jsyk/Talking_Clock/doc/cpuboard_pcb.png

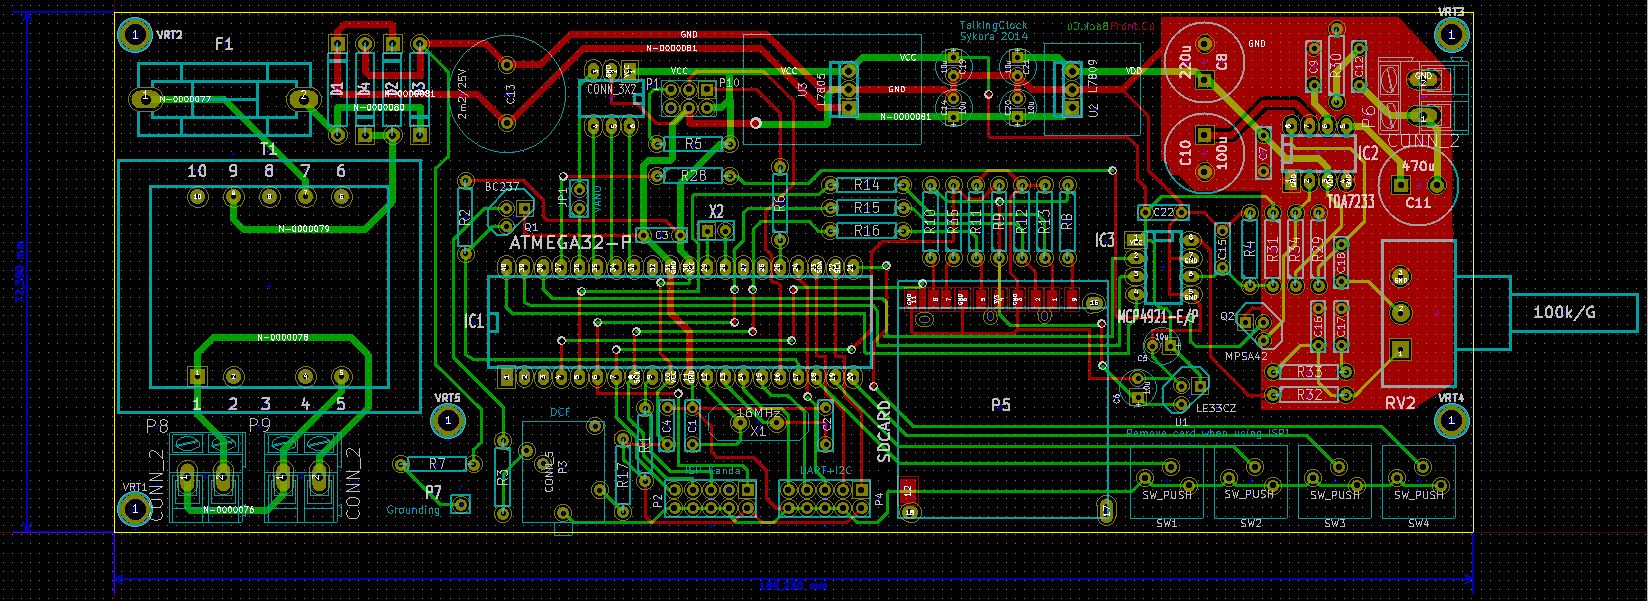
doc/cpuboard_pcb.png
