jsyk/Talking_Clock/doc/cpuboard_sch_atmega.png

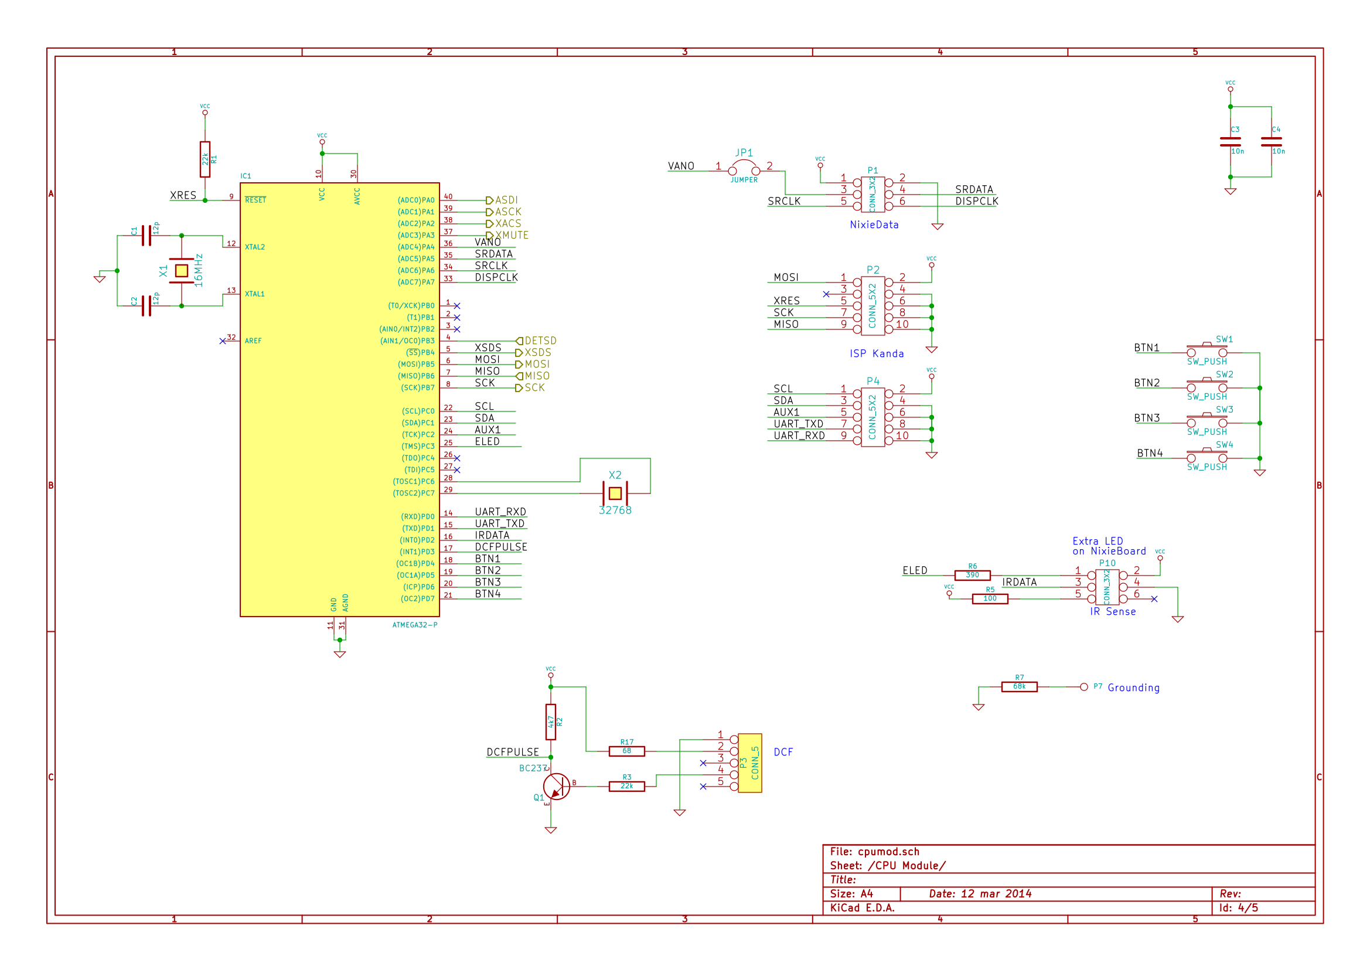
doc/cpuboard_sch_atmega.png
