jsyk/Talking_Clock/doc/cpuboard_sch_power.png

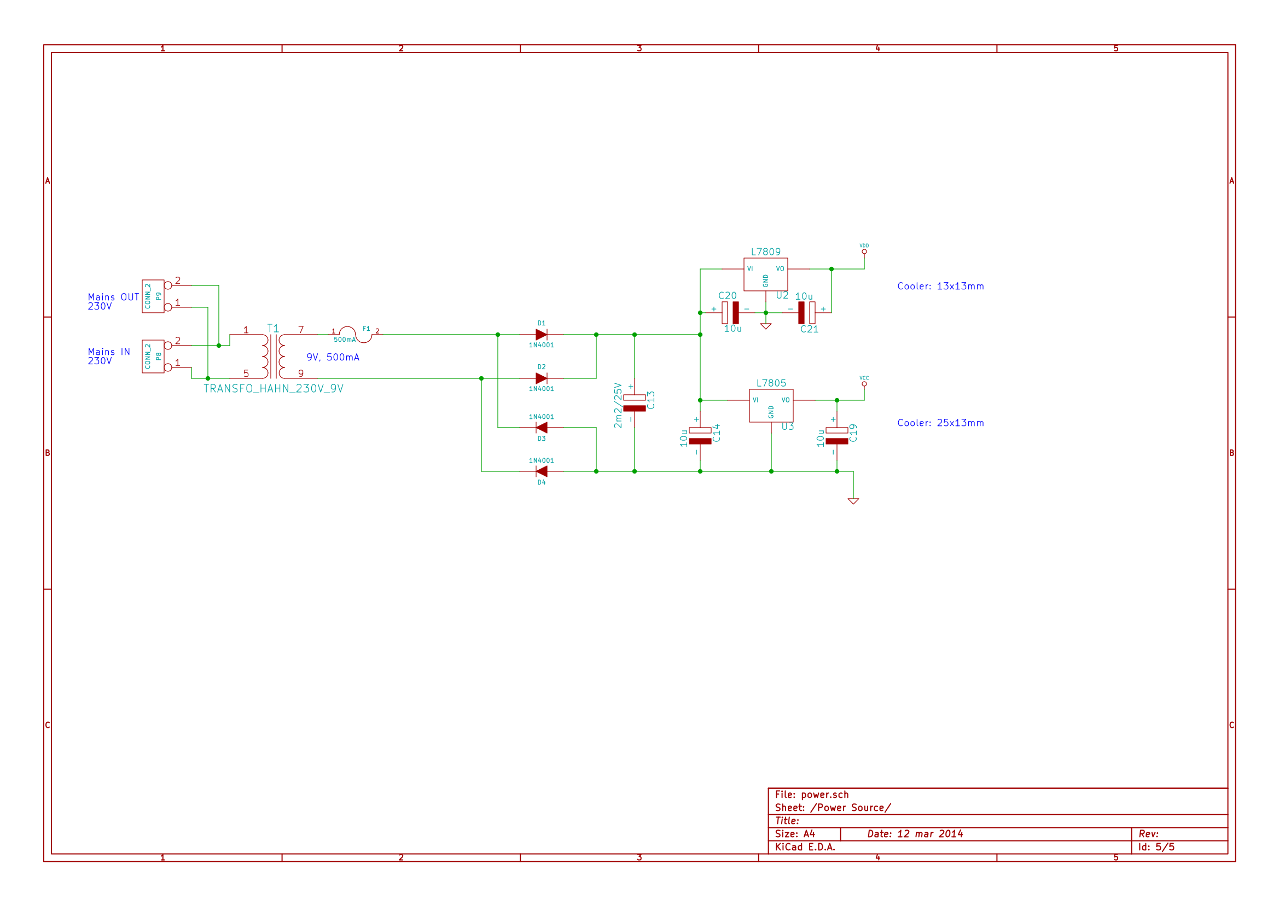
doc/cpuboard_sch_power.png
