jsyk/Talking_Clock/doc/cpuboard_sch_sdcard.png

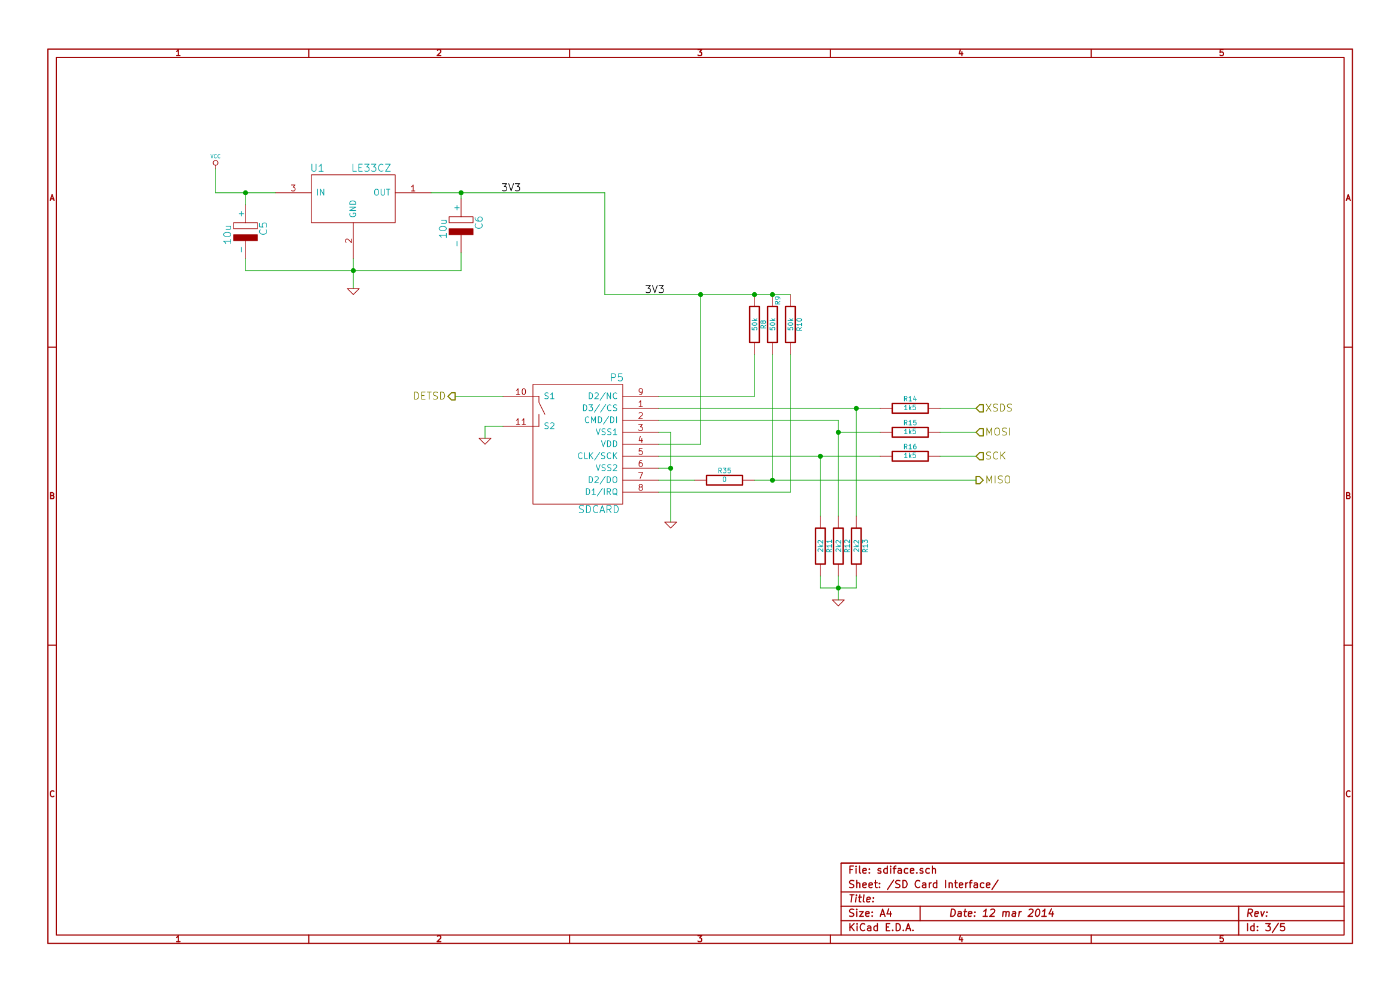
doc/cpuboard_sch_sdcard.png
