jsyk/Talking_Clock/doc/cpuboard_sch_soundsynth.png

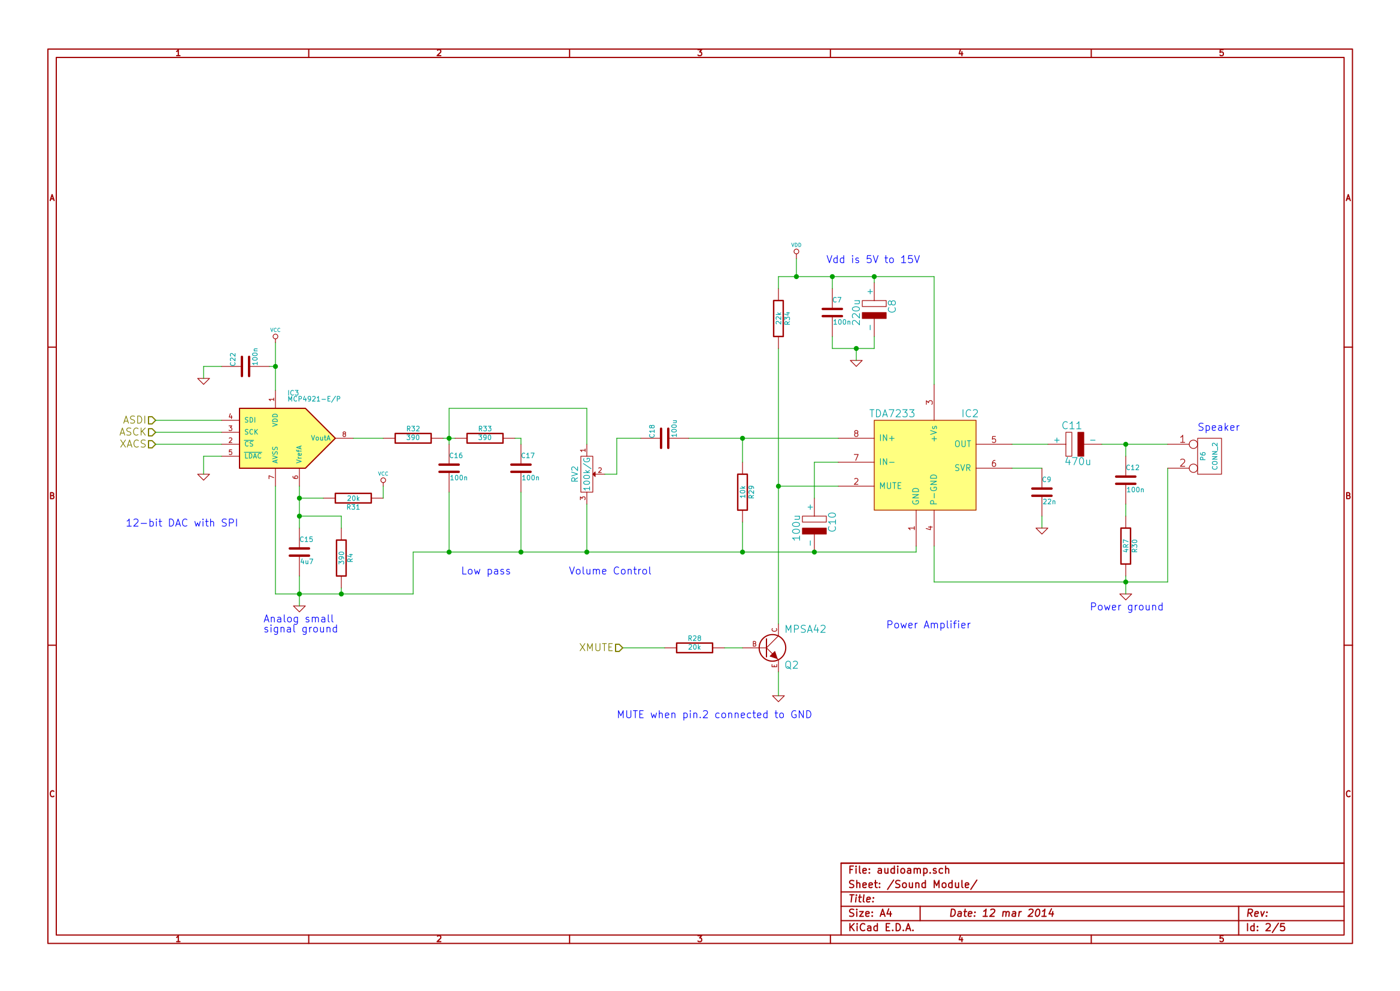
doc/cpuboard_sch_soundsynth.png
