jsyk/Talking_Clock/doc/nixieboard_pcb.png

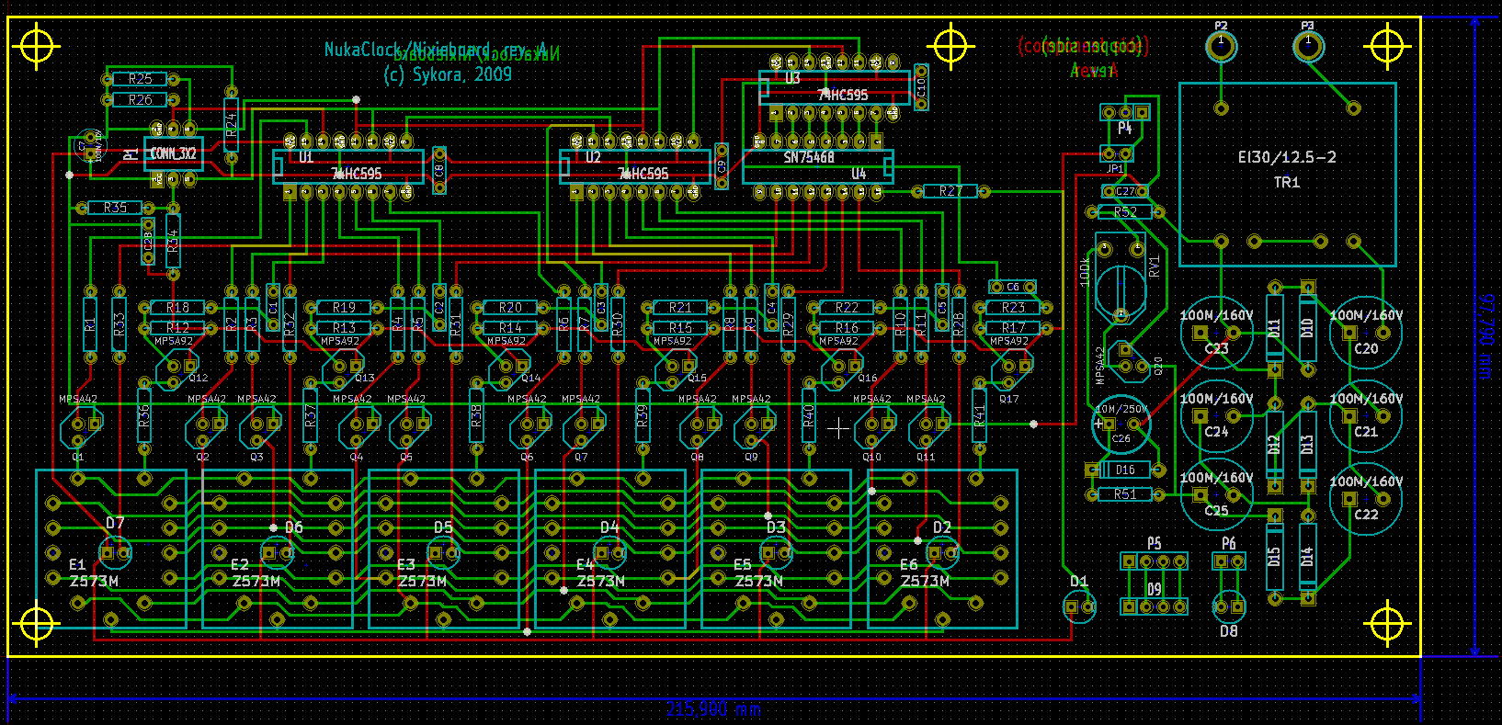
doc/nixieboard_pcb.png
