jsyk/Talking_Clock/doc/nixieboard_sch_drivers.png

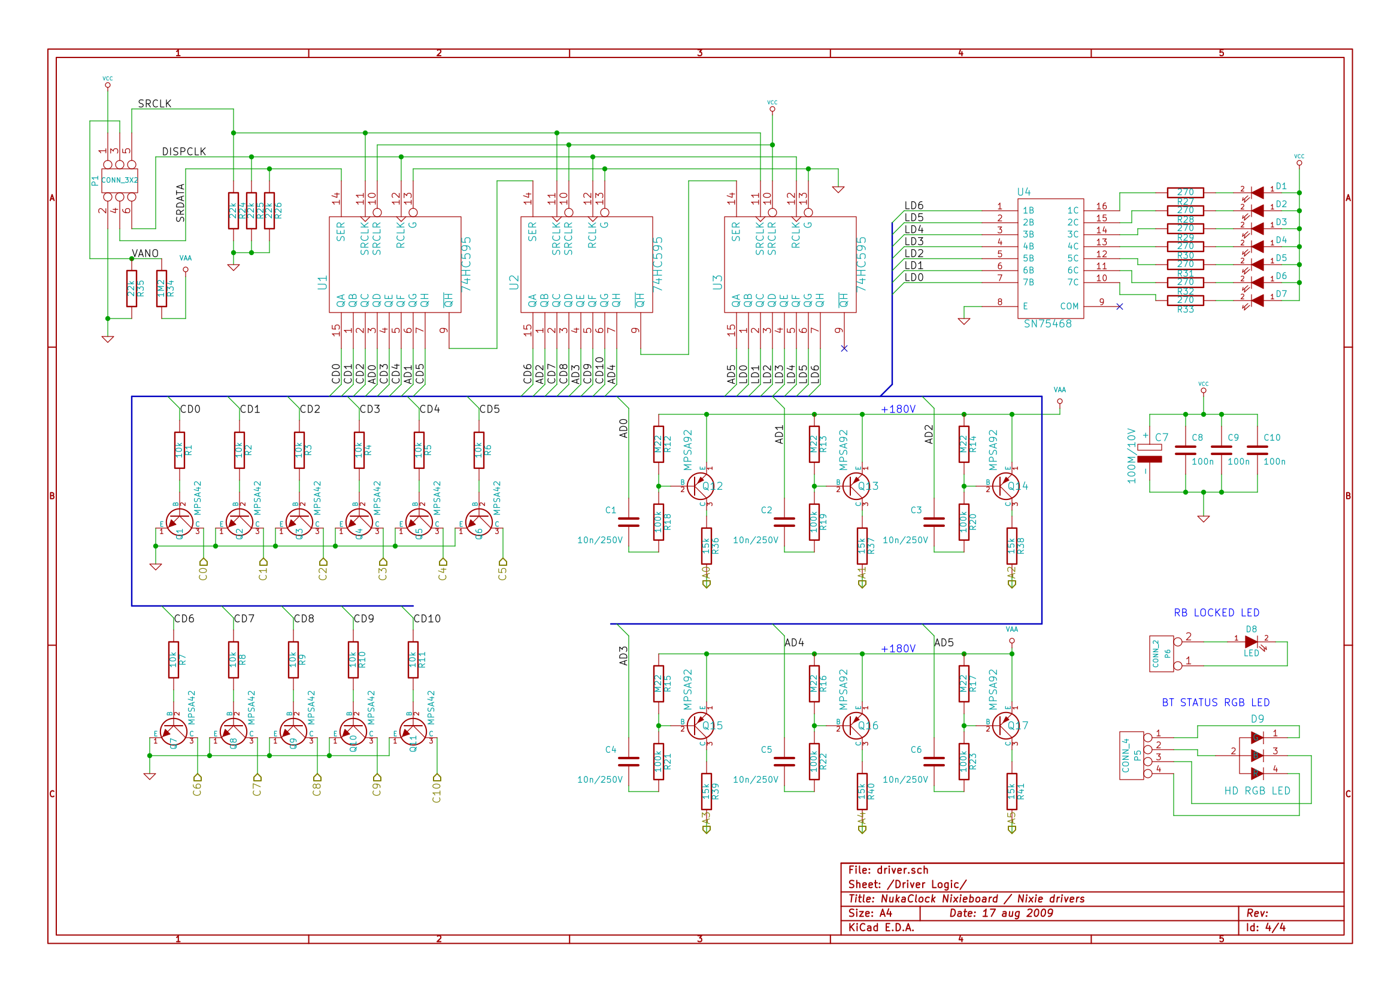
doc/nixieboard_sch_drivers.png
