jsyk/Talking_Clock/doc/nixieboard_sch_hv_power.png

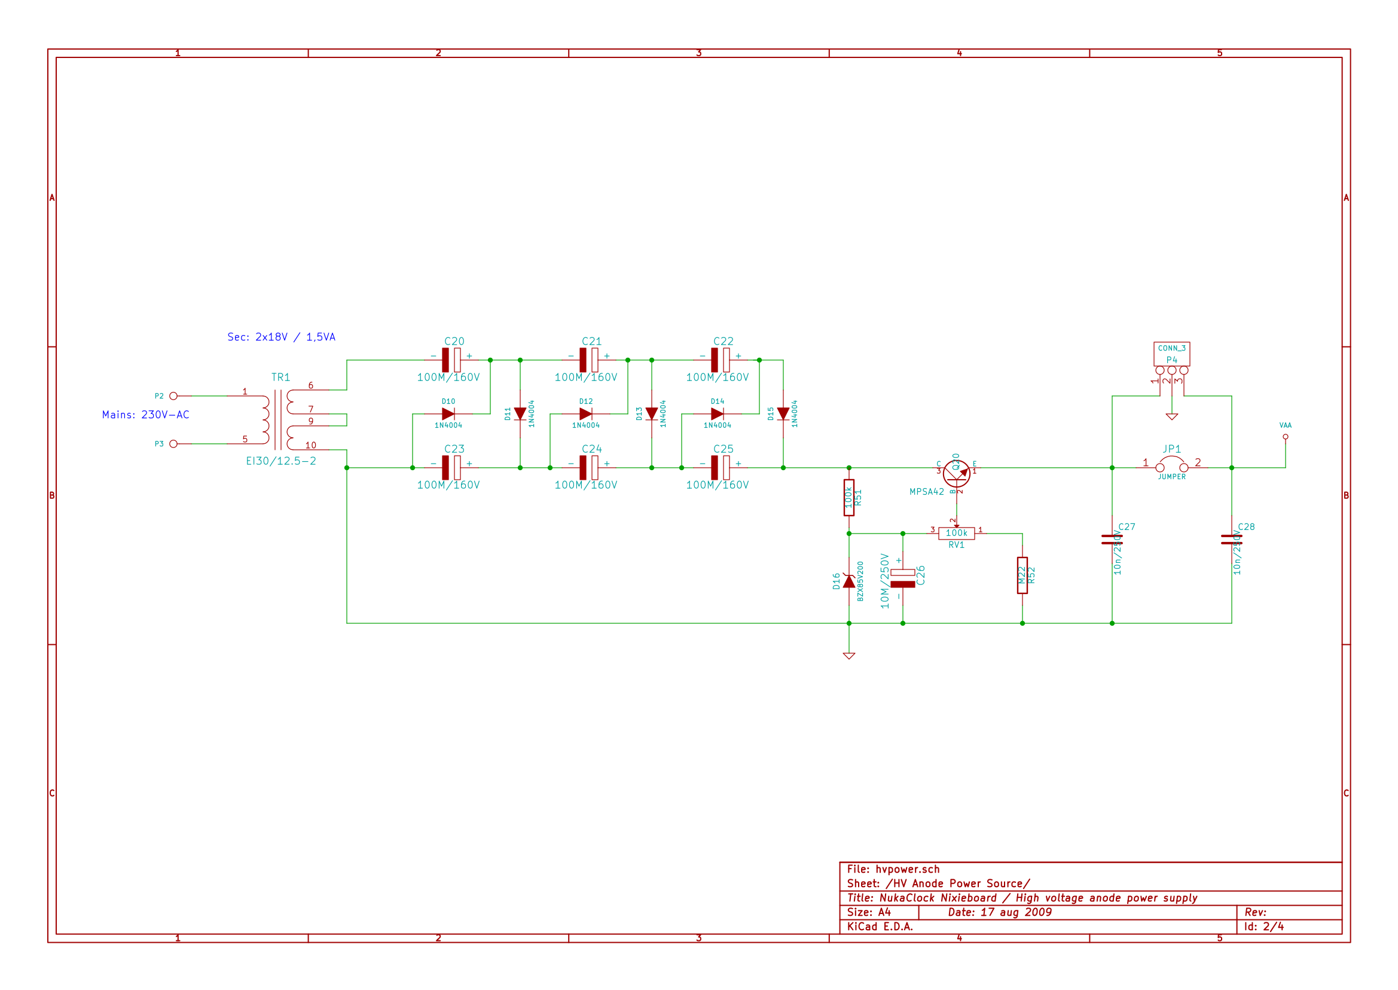
doc/nixieboard_sch_hv_power.png
