jsyk/Talking_Clock/doc/sony_remote.jpg

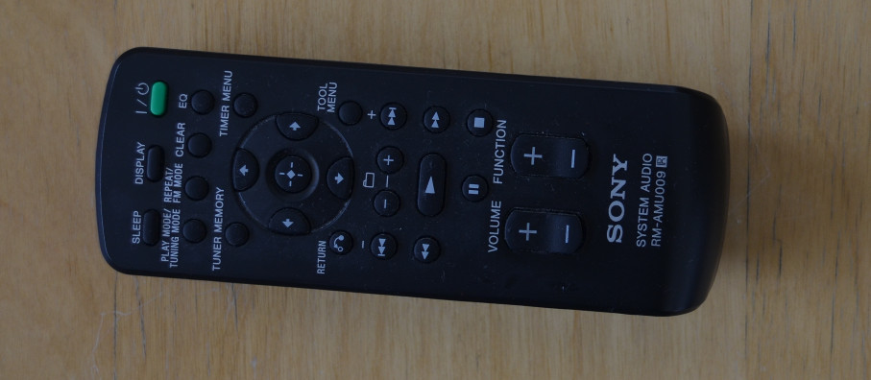
doc/sony_remote.jpg
