jsyk/Talking_Clock/doc/talkingclock_function_scheme.png

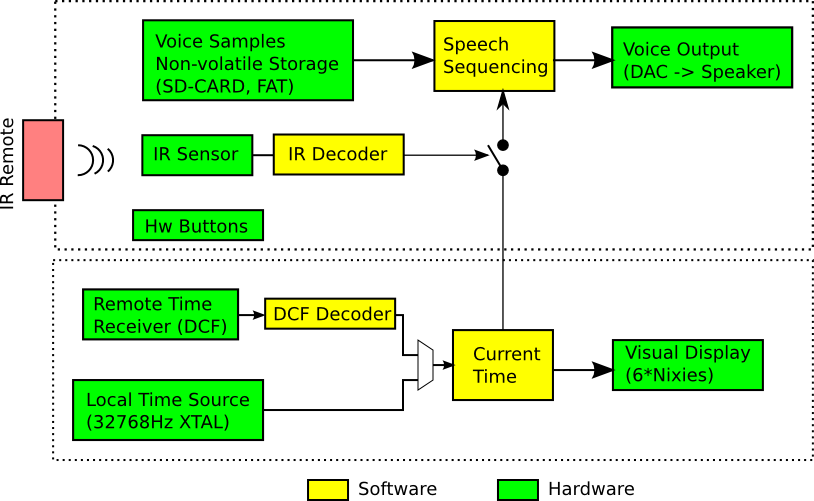
doc/talkingclock_function_scheme.png
