jsyk/Talking_Clock/doc/tc_nixies_closeup.jpg

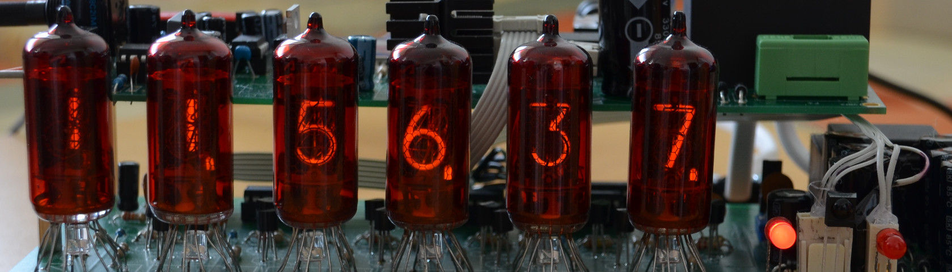
doc/tc_nixies_closeup.jpg
